alexglow/Re-LightBlueBean/Code examples/Original PunchThrough demos/Light_Sensor.cpp

/* 
  This project walks you through adding a phototransistor (light sensor) to your Bean. The sketch will change the intensity and color of the RGB LED based on how much light is detected.

  Circuit assembly:
  Phototransistor from GPIO 0 to A1 (short leg)
  1 megaohm resistor from A1 to GND
    
  Retrieved from: https://web.archive.org/web/20151219142623/http://legacy.punchthrough.com/bean/examples/light-sensor/
    
  This example code is in the public domain.
*/

#define BLEVEL 255
#define MINLEVEL 50

void setup()
{
    // initialize serial communication
    Serial.begin(57600);
    pinMode(0, OUTPUT);     // set D0 as output
    digitalWrite(0, LOW);   // turn it off initially
}

// the loop routine runs over and over again forever:
void loop()
{
    digitalWrite(0, HIGH);
    Bean.sleep(10);
    int sensorValue;
    sensorValue = analogRead(A1);
    int r,g,b;
    if (sensorValue > MINLEVEL && sensorValue < BLEVEL + 1) {
        g = (sensorValue - MINLEVEL)/2;
        b = 0;
    } else if (sensorValue > BLEVEL) {
        g = sensorValue - MINLEVEL;
        if (g > 255) {
            g = 255;
        }
        b = sensorValue-BLEVEL;
        if (b > 255) {
            b = 255;
        }
    } else {
        g = 0;
        b = 0;
    }

    Bean.setLed(0, g, b);
    Bean.sleep(100);          // sleep for a bit
}
